Formlabs/Hackathon-2021-CheckMeet/firmware/stdextra.h

#pragma once

#include <cstdarg>
#include <unordered_map>

template<class T, class... Args>
std::unique_ptr<T> make_unique(Args&&... args)
{
    return std::unique_ptr<T>(new T(std::forward<Args>(args)...));
}

template<class T>
class Span {
    T* m_Data = nullptr;
    size_t m_Size = 0;
public:
    using element_type = T;
    using value_type = typename std::remove_cv<T>::type;
    using size_type = std::size_t;
    using difference_type = std::ptrdiff_t;
    using pointer = T*;
    using const_pointer = const T*;
    using reference = const T&;
    using const_reference = const T&;
    using iterator = T*;
    using reverse_iterator = std::reverse_iterator<iterator>;

    Span() = default;
    Span(T* first, size_type count) : m_Data(first), m_Size(count) {}
    Span(T* first) : m_Data(first), m_Size(std::char_traits<value_type>::length(first)) {}
    template<class ContiguousRange>
    Span(ContiguousRange&& rng) : m_Data(rng.data()), m_Size(rng.size()) {}

    iterator begin() const { return m_Data; }
    iterator end() const { return m_Data + m_Size; }
    pointer data() const { return m_Data; }
    size_type size() const { return m_Size; }
};

using StringView = Span<const char>;

inline StringView operator "" _sv(const char* str, std::size_t len) { return StringView(str, len); }

#ifdef __GNUC__
__attribute__((format(printf, 1, 2)))
#endif
inline std::string fmt(const char* format, ...) {
    va_list args1;
    va_start(args1, format);
    va_list args2;
    va_copy(args2, args1);
    const auto len = vsnprintf(nullptr, 0, format, args1);
    va_end(args1);
    std::string result(len, '\0'); // from C++11 this provides (len+1) sized storage
    vsnprintf(&result.front(), result.size() + 1, format, args2);
    va_end(args2);
    return result;
}

template< class Key, class T, class Hash, class KeyEqual, class Alloc, class Pred >
typename std::unordered_map<Key, T, Hash, KeyEqual, Alloc>::size_type
erase_if(std::unordered_map<Key, T, Hash, KeyEqual, Alloc>& c, Pred pred) {
    auto old_size = c.size();
    for (auto i = c.begin(), last = c.end(); i != last; ) {
        if (pred(*i)) {
            i = c.erase(i);
        }
        else {
            ++i;
        }
    }
    return old_size - c.size();
}
